ThomasChevalier/passwordWallet/Code/src/Hardware/Hardware.h

#ifndef HARDWARE_HEADER_THOMAS_CHEVALIER
#define HARDWARE_HEADER_THOMAS_CHEVALIER
 
/**
 * @brief Init all the hardware io and call the initialization function of oled and spi.
 */
void hardware_init(void);

#endif // HARDWARE_HEADER_THOMAS_CHEVALIER
