ThomasChevalier/passwordWallet/Code/src/Hardware/Oled.c

#include "Oled.h"

#include "../Globals.h"

#include "PinDefinition.h"
#include "Spi.h"

#if defined(STORE_SCREEN_BUFFER_IN_FRAM)
#include "Fram.h"
#endif

#define WIDTH 128
#define HEIGHT 64

#ifndef STORE_SCREEN_BUFFER_IN_FRAM
uint8_t oled_data[SSD1306_LCDHEIGHT * SSD1306_LCDWIDTH / 8] =
{
	0x00, 0x00, 0x00, 0x00, 0x00, 0x00, 0x00, 0x00, 0x00, 0x00, 0x00, 0x00, 0x00, 0x00, 0x00, 0x00,
	0x00, 0x00, 0x00, 0x80, 0xC0, 0xC0, 0xE0, 0x70, 0x70, 0x00, 0x00, 0x00, 0x00, 0x00, 0x00, 0x00,
	0x00, 0x00, 0x00, 0x00, 0x00, 0x00, 0x00, 0x00, 0x00, 0x00, 0x00, 0x00, 0x00, 0x00, 0x00, 0x00,
	0x00, 0x80, 0xE0, 0xF0, 0xF8, 0xF8, 0xFC, 0xFC, 0xFE, 0xFE, 0xFF, 0xFF, 0xFF, 0xFF, 0xFF, 0xFF,
	0xFF, 0xFF, 0xFF, 0xFF, 0xFF, 0xFE, 0xFE, 0xFC, 0xFC, 0xF8, 0xF0, 0xF0, 0xC0, 0x80, 0x00, 0x00,
	0x00, 0x00, 0x00, 0x00, 0x00, 0x00, 0x00, 0x00, 0x00, 0x00, 0x00, 0x00, 0x00, 0x00, 0x00, 0x00,
	0x00, 0x00, 0x00, 0x00, 0x00, 0x00, 0x70, 0x70, 0xE0, 0xC0, 0xC0, 0x80, 0x00, 0x00, 0x00, 0x00,
	0x00, 0x00, 0x00, 0x00, 0x00, 0x00, 0x00, 0x00, 0x00, 0x00, 0x00, 0x00, 0x00, 0x00, 0x00, 0x00,
	0x00, 0x00, 0x00, 0x00, 0x00, 0x00, 0x00, 0x00, 0x00, 0x00, 0x00, 0x00, 0x00, 0x80, 0xE0, 0xF0,
	0x78, 0x1E, 0x0F, 0x07, 0x03, 0x01, 0x00, 0x00, 0x80, 0xC0, 0xE0, 0xF0, 0x70, 0x38, 0x18, 0x00,
	0x00, 0x00, 0x00, 0x00, 0x00, 0x00, 0x00, 0x00, 0x00, 0x00, 0x00, 0x00, 0x00, 0x00, 0xC0, 0xFC,
	0xFF, 0xFF, 0xFF, 0xFF, 0xFF, 0xFF, 0x3F, 0x0F, 0x03, 0x01, 0x01, 0x00, 0x00, 0x00, 0x00, 0x00,
	0x00, 0x00, 0x00, 0x00, 0x01, 0x03, 0x07, 0x0F, 0x7F, 0xFF, 0xFF, 0xFF, 0xFF, 0xFF, 0xFE, 0xF8,
	0x80, 0x00, 0x00, 0x00, 0x00, 0x00, 0x00, 0x00, 0x00, 0x00, 0x00, 0x00, 0x00, 0x00, 0x00, 0x00,
	0x18, 0x38, 0x70, 0xF0, 0xE0, 0xC0, 0x80, 0x00, 0x00, 0x01, 0x03, 0x07, 0x0F, 0x1E, 0x7C, 0xF0,
	0xE0, 0x80, 0x00, 0x00, 0x00, 0x00, 0x00, 0x00, 0x00, 0x00, 0x00, 0x00, 0x00, 0x00, 0x00, 0x00,
	0x00, 0x00, 0x00, 0x00, 0x00, 0x00, 0x00, 0x00, 0x00, 0x00, 0xE0, 0xF8, 0xFE, 0x1F, 0x03, 0x00,
	0x00, 0x00, 0x00, 0x80, 0xE0, 0xF8, 0x3E, 0x0F, 0x07, 0x03, 0x01, 0x00, 0x00, 0x80, 0xC0, 0xE0,
	0x70, 0x38, 0x38, 0x1C, 0x08, 0x00, 0x00, 0x00, 0x00, 0x00, 0x00, 0x00, 0x00, 0x00, 0x3F, 0x3F,
	0x3F, 0x3F, 0x3F, 0x3F, 0x3F, 0x3F, 0x00, 0x00, 0x00, 0x00, 0x00, 0x00, 0x00, 0x00, 0x00, 0x00,
	0x00, 0x00, 0x00, 0x00, 0x00, 0x00, 0x00, 0x00, 0x00, 0x3F, 0x3F, 0x3F, 0x3F, 0x3F, 0x3F, 0x3F,
	0x3F, 0x00, 0x00, 0x00, 0x00, 0x00, 0x00, 0x00, 0x00, 0x00, 0x08, 0x1C, 0x38, 0x38, 0x70, 0xE0,
	0xC0, 0x80, 0x00, 0x00, 0x01, 0x03, 0x07, 0x0F, 0x3E, 0xF8, 0xE0, 0x80, 0x00, 0x00, 0x00, 0x00,
	0x03, 0x1F, 0xFE, 0xF8, 0xE0, 0x00, 0x00, 0x00, 0x00, 0x00, 0x00, 0x00, 0x00, 0x00, 0x00, 0x00,
	0x00, 0x00, 0x00, 0x00, 0x00, 0x00, 0x00, 0x00, 0x00, 0xFC, 0xFF, 0xFF, 0x00, 0x00, 0x00, 0x00,
	0x00, 0x00, 0xFC, 0xFF, 0xFF, 0x01, 0x00, 0x00, 0x00, 0x00, 0x00, 0xF8, 0xFE, 0xFF, 0x03, 0x01,
	0x00, 0x00, 0x00, 0x00, 0x00, 0x00, 0x00, 0xF0, 0xF8, 0xFC, 0xFE, 0xFE, 0xFE, 0xFF, 0xFF, 0xFF,
	0xFF, 0xFF, 0xFF, 0xFF, 0xFF, 0xFF, 0xFF, 0xFF, 0xFF, 0xFF, 0xFF, 0xFF, 0xFF, 0xFF, 0xFF, 0xFF,
	0xFF, 0xFF, 0xFF, 0xFF, 0xFF, 0xFF, 0xFF, 0xFF, 0xFF, 0xFF, 0xFF, 0xFF, 0xFF, 0xFF, 0xFF, 0xFF,
	0xFF, 0xFF, 0xFE, 0xFE, 0xFE, 0xFC, 0xF8, 0xE0, 0x00, 0x00, 0x00, 0x00, 0x00, 0x00, 0x00, 0x01,
	0x03, 0xFF, 0xFE, 0xF8, 0x00, 0x00, 0x00, 0x00, 0x00, 0x01, 0xFF, 0xFF, 0xFC, 0x00, 0x00, 0x00,
	0x00, 0x00, 0x00, 0xFF, 0xFF, 0xFC, 0x00, 0x00, 0x00, 0x00, 0x00, 0x00, 0x00, 0x00, 0x00, 0x00,
	0x00, 0x00, 0x00, 0x00, 0x00, 0x00, 0x00, 0x00, 0x00, 0x0F, 0xFF, 0xFF, 0xC0, 0x00, 0x00, 0x00,
	0x00, 0x00, 0x0F, 0x7F, 0xFF, 0xE0, 0x00, 0x00, 0x00, 0x00, 0x00, 0x07, 0x1F, 0x7F, 0xF0, 0xE0,
	0x80, 0x00, 0x00, 0x00, 0x00, 0x00, 0x00, 0xFF, 0xFF, 0xFF, 0xFF, 0xFF, 0xFF, 0xFF, 0xFF, 0xFF,
	0xFF, 0xFF, 0xFF, 0xFF, 0xFF, 0xFF, 0xFF, 0xFF, 0xFF, 0xFF, 0xFF, 0x7F, 0x3F, 0x3F, 0x1F, 0x1F,
	0x1F, 0x3F, 0x3F, 0xFF, 0xFF, 0xFF, 0xFF, 0xFF, 0xFF, 0xFF, 0xFF, 0xFF, 0xFF, 0xFF, 0xFF, 0xFF,
	0xFF, 0xFF, 0xFF, 0xFF, 0xFF, 0xFF, 0xFF, 0xFF, 0x00, 0x00, 0x00, 0x00, 0x00, 0x00, 0x80, 0xE0,
	0xF0, 0x7F, 0x1F, 0x07, 0x00, 0x00, 0x00, 0x00, 0x00, 0xE0, 0xFF, 0x7F, 0x0F, 0x00, 0x00, 0x00,
	0x00, 0x00, 0xC0, 0xFF, 0xFF, 0x0F, 0x00, 0x00, 0x00, 0x00, 0x00, 0x00, 0x00, 0x00, 0x00, 0x00,
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
};
#endif

static uint8_t reverse(uint8_t b) {
	b = (b & 0xF0) >> 4 | (b & 0x0F) << 4;
	b = (b & 0xCC) >> 2 | (b & 0x33) << 2;
	b = (b & 0xAA) >> 1 | (b & 0x55) << 1;
	return b;
}


// Hardware

// Thoses functions are only one instruction long (inline them)
/**
 * @brief Pull the data/command pin high.
 */
#define oled_dc_high() (OLED_DC_PORT |= (1 << OLED_DC_PIN_NUM))

/**
 * @brief Pull the data/command pin low.
 */
#define oled_dc_low() (OLED_DC_PORT &= ~(1 << OLED_DC_PIN_NUM))

/**
 * @brief Pull the reset pin high.
 */
#define oled_reset_high() (OLED_RES_PORT |= (1 << OLED_RES_PIN_NUM))

/**
 * @brief Pull the reset pin low.
 */
#define oled_reset_low() (OLED_RES_PORT &= ~(1 << OLED_RES_PIN_NUM))

/**
 * @brief Pull the CS pin high.
 */
#define oled_deselect() (OLED_CS_PORT |= (1 << OLED_CS_PIN_NUM))

/**
 * @brief Pull the CS pin low.
 */
#define oled_select() (OLED_CS_PORT &= ~(1 << OLED_CS_PIN_NUM))


// Software

/**
 * @brief Send a command to the oled display.
 * @details Use it if you really know what you are doing.
 * 
 * @param c The byte to send as a command.
 */
static void oled_command(uint8_t c)
{
	oled_deselect();
	oled_dc_low();
	oled_select();
	spi_send_8(c);
	oled_deselect();
}

static const __flash uint8_t oled_init_cmd[] =
{
	SSD1306_DISPLAYOFF,
	SSD1306_SETDISPLAYCLOCKDIV,
	0x80,
	SSD1306_SETMULTIPLEX,
	SSD1306_LCDHEIGHT - 1,
	SSD1306_SETDISPLAYOFFSET,
	0x0,
	SSD1306_SETSTARTLINE | 0x0,
	SSD1306_CHARGEPUMP,
	0x14,
	SSD1306_MEMORYMODE,
	0x00,
	SSD1306_SEGREMAP | 0x1,
	SSD1306_COMSCANDEC,
	SSD1306_SETCOMPINS,
	0x12,
	SSD1306_SETCONTRAST,
	0xCF,
	SSD1306_SETPRECHARGE,
	0xF1,
	SSD1306_SETVCOMDETECT,
	0x40,
	SSD1306_DISPLAYALLON_RESUME,
	SSD1306_NORMALDISPLAY,
	SSD1306_DEACTIVATE_SCROLL,
	SSD1306_DISPLAYON
};

void oled_init()
{
	oled_reset_high();
	delay_ms_f(1);
	// bring reset low
	oled_reset_low();

	// wait 10ms
	delay_ms_f(10);
	// bring out of reset
	oled_reset_high();

	// Init sequence
	for(uint8_t i = 0; i < 26; ++i)
	{
		oled_command(oled_init_cmd[i]);
	}
}

// the most basic function, set a single pixel
void oled_draw_pixel(uint8_t x, uint8_t y, uint8_t color)
{
	if(x >= 128 || y >= 64)
		return;

	// x is which column
	#ifdef STORE_SCREEN_BUFFER_IN_FRAM

	uint8_t buf = fram_read_byte(OFFSET_OLED_BUFFER + (x+ (y/8)*WIDTH));
	uint8_t val = (1 << (y&7));
	switch (color)
	{
	case WHITE:
		buf |= val;
		break;
	case BLACK:
		buf &= ~val;
		break;
	case INVERSE:
		buf ^= val;
		break;
	}
	fram_write_byte(OFFSET_OLED_BUFFER + (x+ (y/8)*WIDTH), buf);

	#else

	uint8_t* buf = &oled_data[x+ (y/8)*WIDTH];
	uint8_t val = (1 << (y&7));
	switch (color)
	{
	case WHITE:
		(*buf) |=  val;
		break;
	case BLACK:
		(*buf) &= ~val;
		break;
	case INVERSE:
		(*buf) ^=  val;
		break;
	}

	#endif
}

void oled_invert_display(uint8_t i)
{
	oled_command(i ? SSD1306_INVERTDISPLAY : SSD1306_NORMALDISPLAY);
}

// Dim the display
// dim = true: display is dimmed
// dim = false: display is normal
void oled_dim(uint8_t dim)
{
	// the range of contrast to too small to be really useful
	// it is useful to dim the display
	oled_command(SSD1306_SETCONTRAST);
	oled_command(dim ? 0 : 0xCF);
}

void oled_display(void)
{
	oled_command(SSD1306_COLUMNADDR);
	oled_command(0);   // Column start address (0 = reset)
	oled_command(SSD1306_LCDWIDTH-1);  // Column end address (127 = reset)

	oled_command(SSD1306_PAGEADDR);
	oled_command(0);  // Page start address (0 = reset)

	oled_command(7);  // Page end address

	oled_deselect();
	oled_dc_high();
	oled_select();

	#ifdef STORE_SCREEN_BUFFER_IN_FRAM
	uint8_t pixBuff[64];

	uint8_t i = 0;
	uint8_t j = 0;
	for(; i < ((HEIGHT * WIDTH / 8) / 64); ++i)
	{
		oled_deselect();
		fram_read_bytes(OFFSET_OLED_BUFFER + i*64, pixBuff, 64);
		oled_select();
		for(j = 0; j < 64; ++j)
		{
			// This does not manage screen orientation
			spi_send_8(pixBuff[j]);
		}
	}
	#else

	uint16_t i = 0;
	const uint16_t totalSize = SSD1306_LCDHEIGHT * SSD1306_LCDWIDTH / 8;
	for (; i < (HEIGHT * WIDTH / 8); ++i)
	{
		if(OPTIONS_FLAG & (1 << OPTIONS_FLAG_OFFSET_ORIENTATION))
		{
			spi_send_8(reverse(oled_data[totalSize-i-1]));
		}
		else{
			spi_send_8(oled_data[i]);
		}
	}
	#endif

	oled_deselect();
}

// clear everything
void oled_clear_display(void)
{
	#ifdef STORE_SCREEN_BUFFER_IN_FRAM
	uint8_t i = 0;
	for(; i < ((HEIGHT * WIDTH / 8) / 128); ++i)
	{
		fram_set(i*128, 0, 128);
	}
	#else
	uint16_t i = 0;
	for (; i < (HEIGHT * WIDTH / 8); ++i)
	{
		oled_data[i] = 0;
	}
	#endif
}

void oled_active_display(uint8_t active)
{
	if(active)
	{
		oled_command(SSD1306_DISPLAYON);
	}
	else
	{
		oled_command(SSD1306_DISPLAYOFF);
	}
}
